dpaulb005/radar-dev-/3d/renders/drone/exploded.png

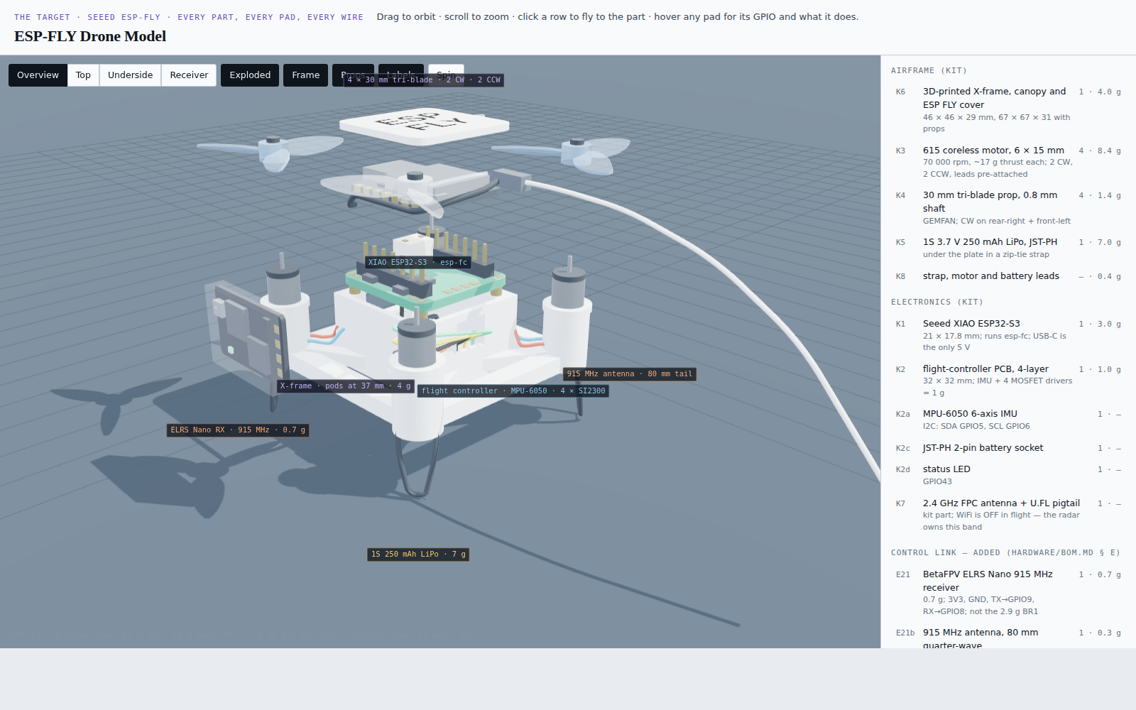
3d/renders/drone/exploded.png
