dpaulb005/radar-dev-/3d/renders/drone/receiver.png

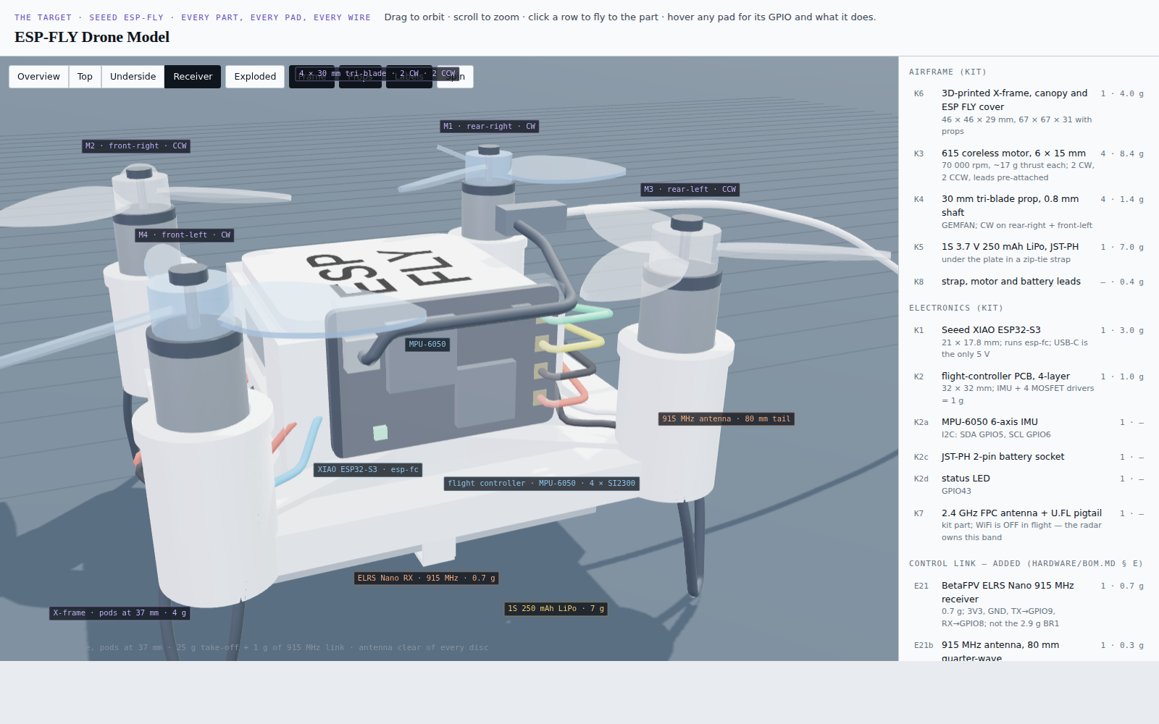
3d/renders/drone/receiver.png
