dpaulb005/radar-dev-/3d/renders/drone/top.png

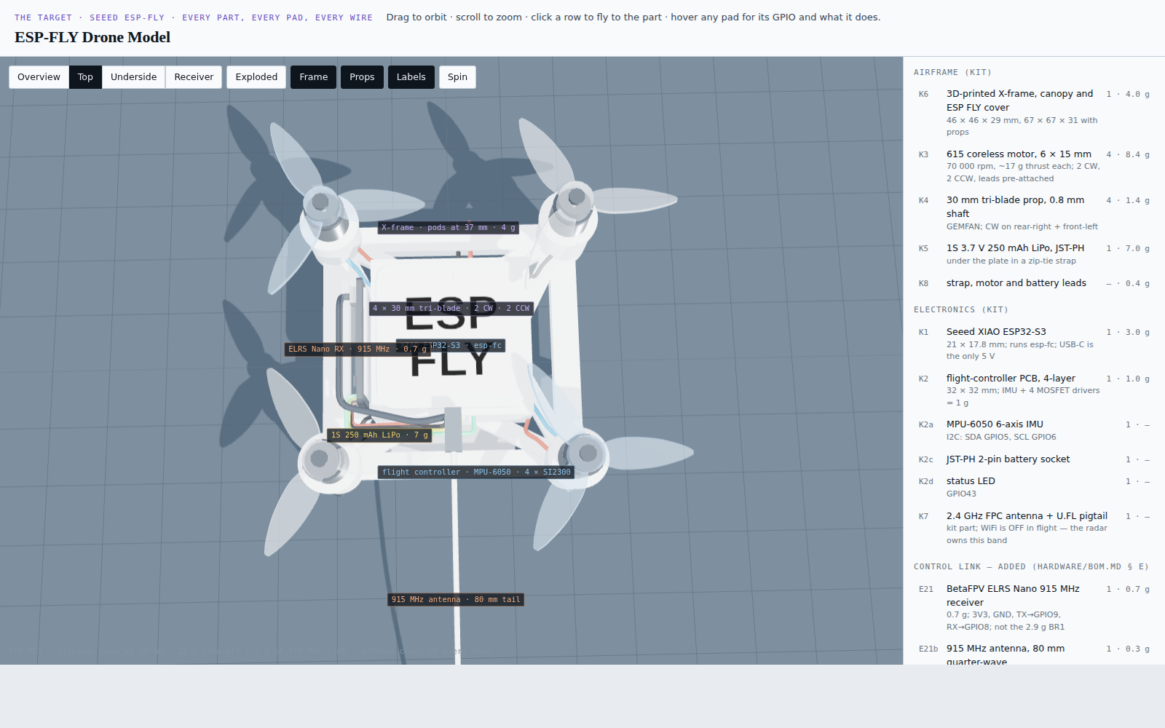
3d/renders/drone/top.png
