dpaulb005/radar-dev-/3d/renders/drone/underside.png

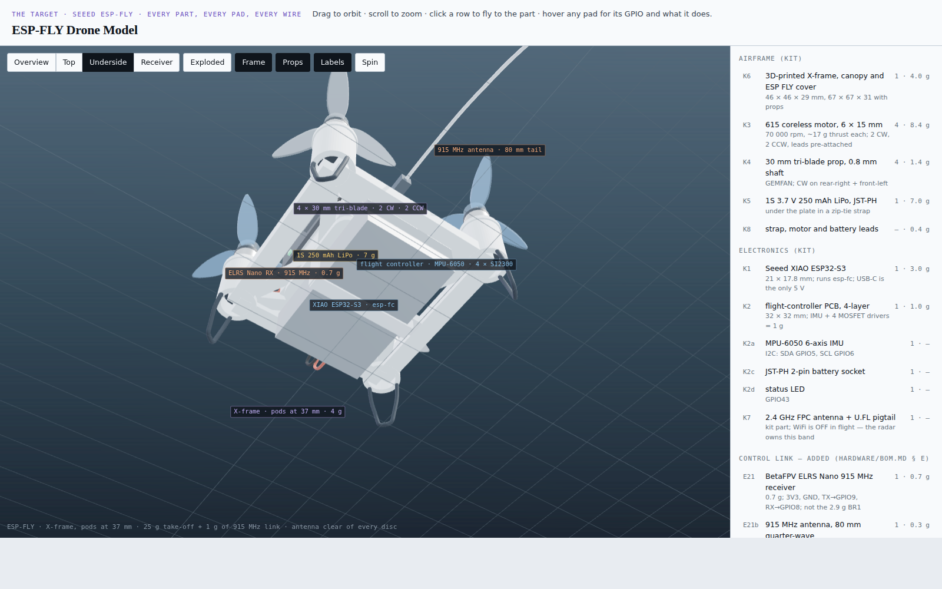
3d/renders/drone/underside.png
