dpaulb005/radar-dev-/3d/renders/radar-bench/bench.png

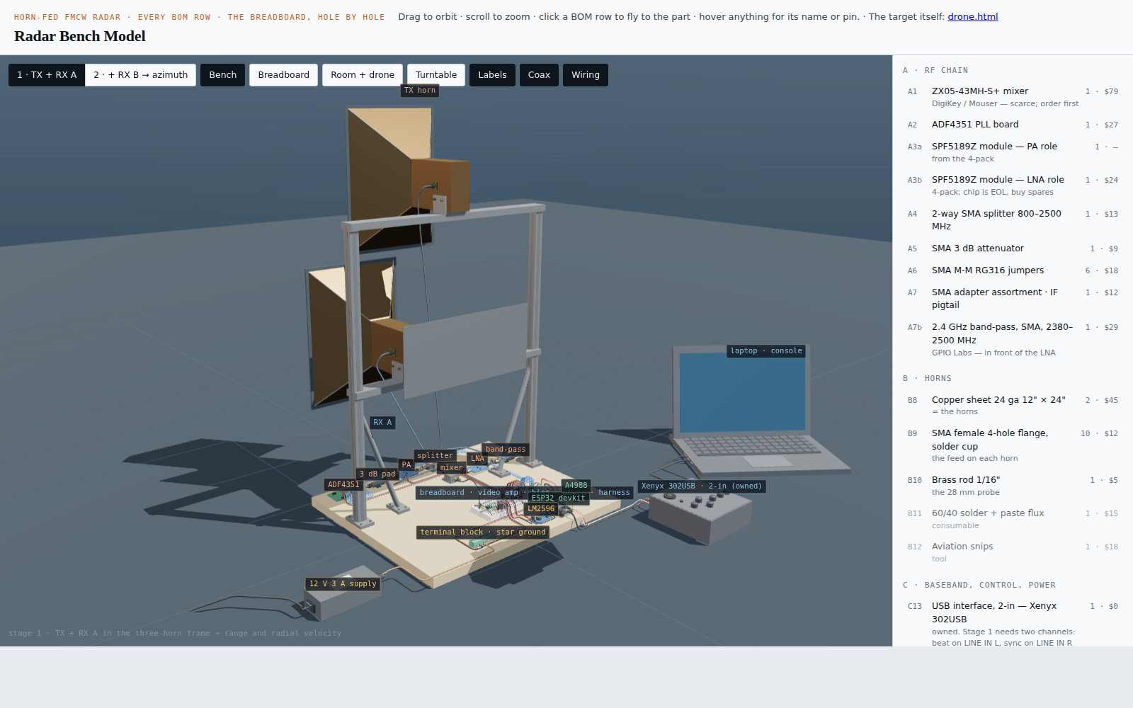
3d/renders/radar-bench/bench.png
