dpaulb005/radar-dev-/3d/renders/radar-bench/breadboard.png

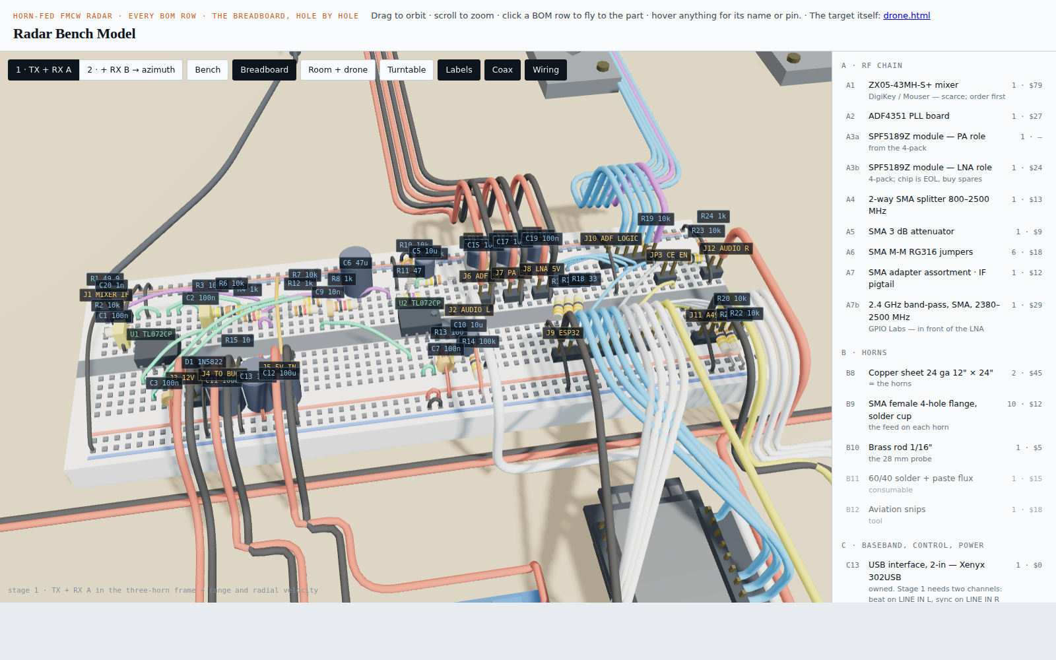
3d/renders/radar-bench/breadboard.png
