dpaulb005/radar-dev-/3d/renders/radar-bench/desk.png

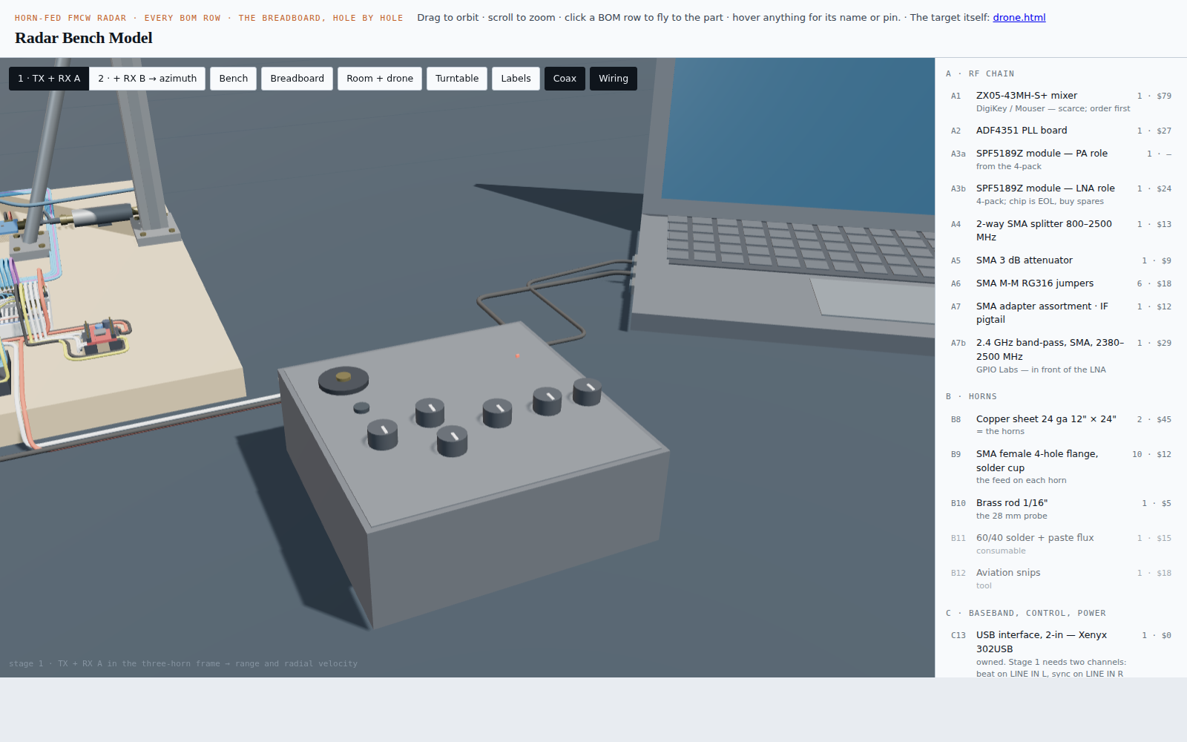
3d/renders/radar-bench/desk.png
