dpaulb005/radar-dev-/3d/renders/radar-bench/plan.png

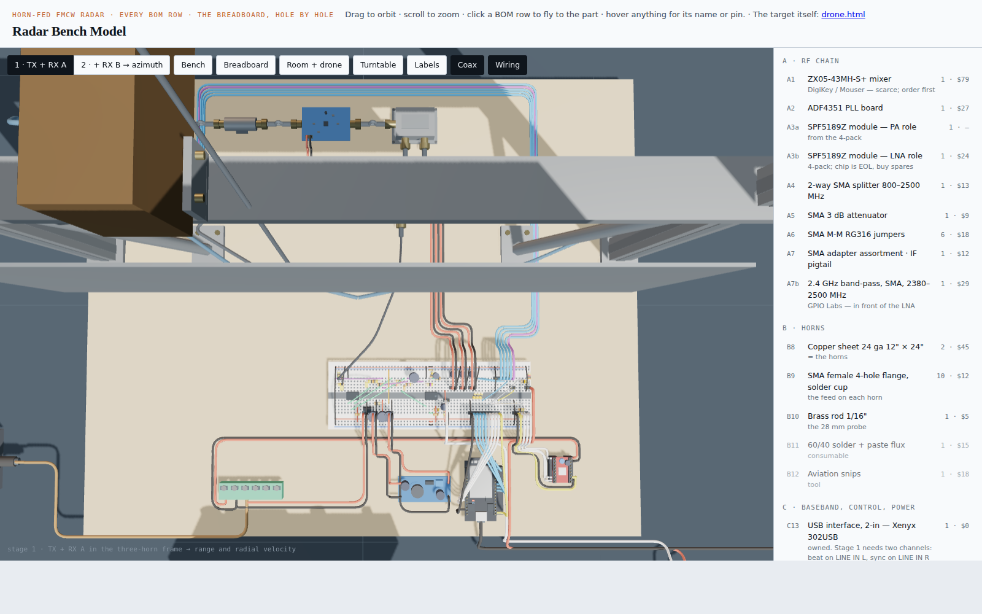
3d/renders/radar-bench/plan.png
