dpaulb005/radar-dev-/3d/renders/radar-bench/room.png

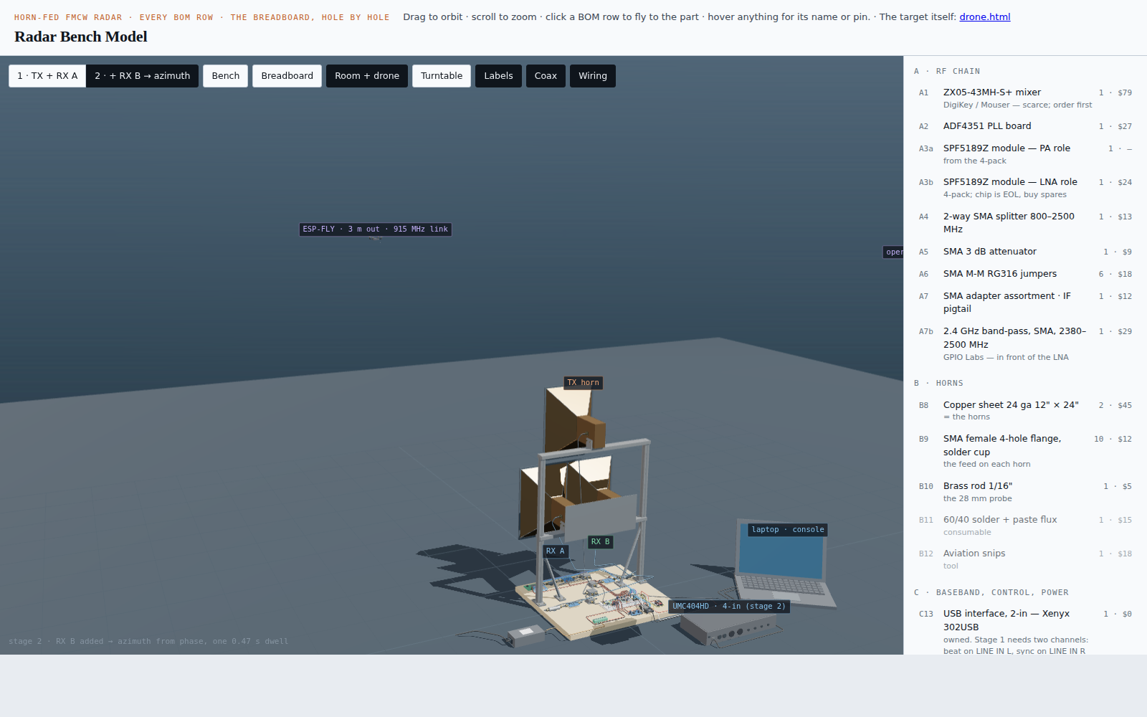
3d/renders/radar-bench/room.png
