dpaulb005/radar-dev-/3d/renders/radar-bench/stage2.png

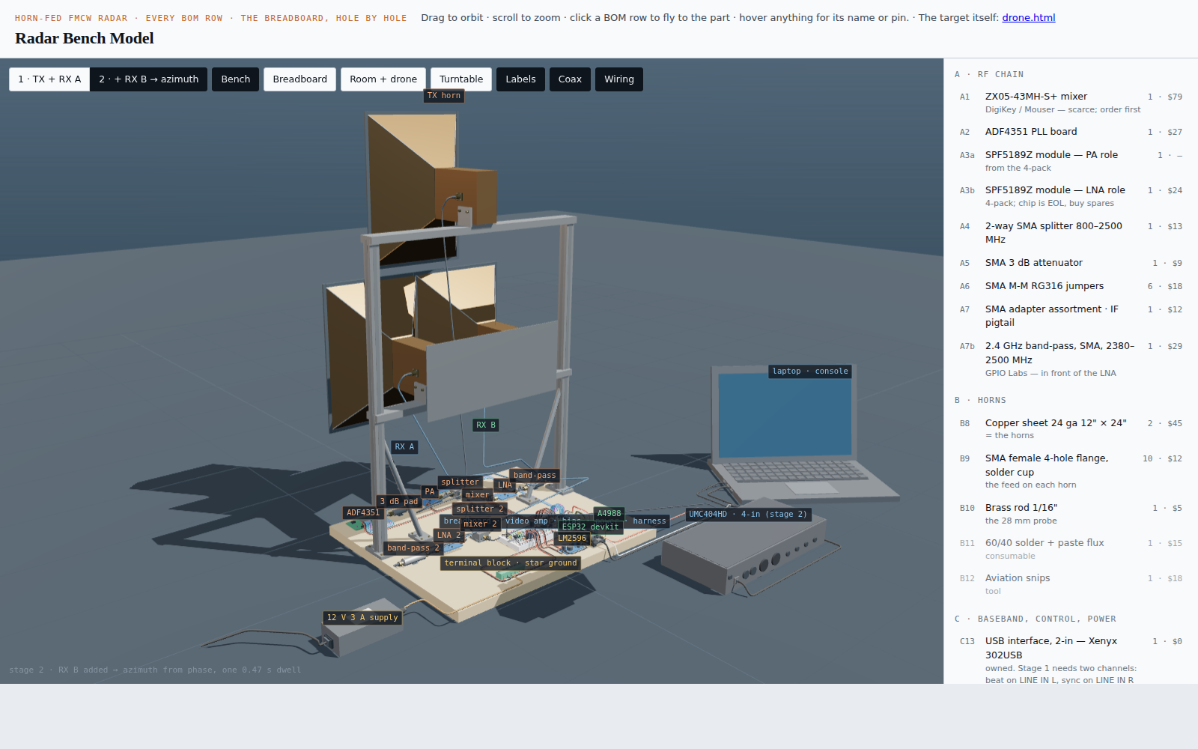
3d/renders/radar-bench/stage2.png
