dpaulb005/radar-dev-/breadboard/schematics/radar_flow.png

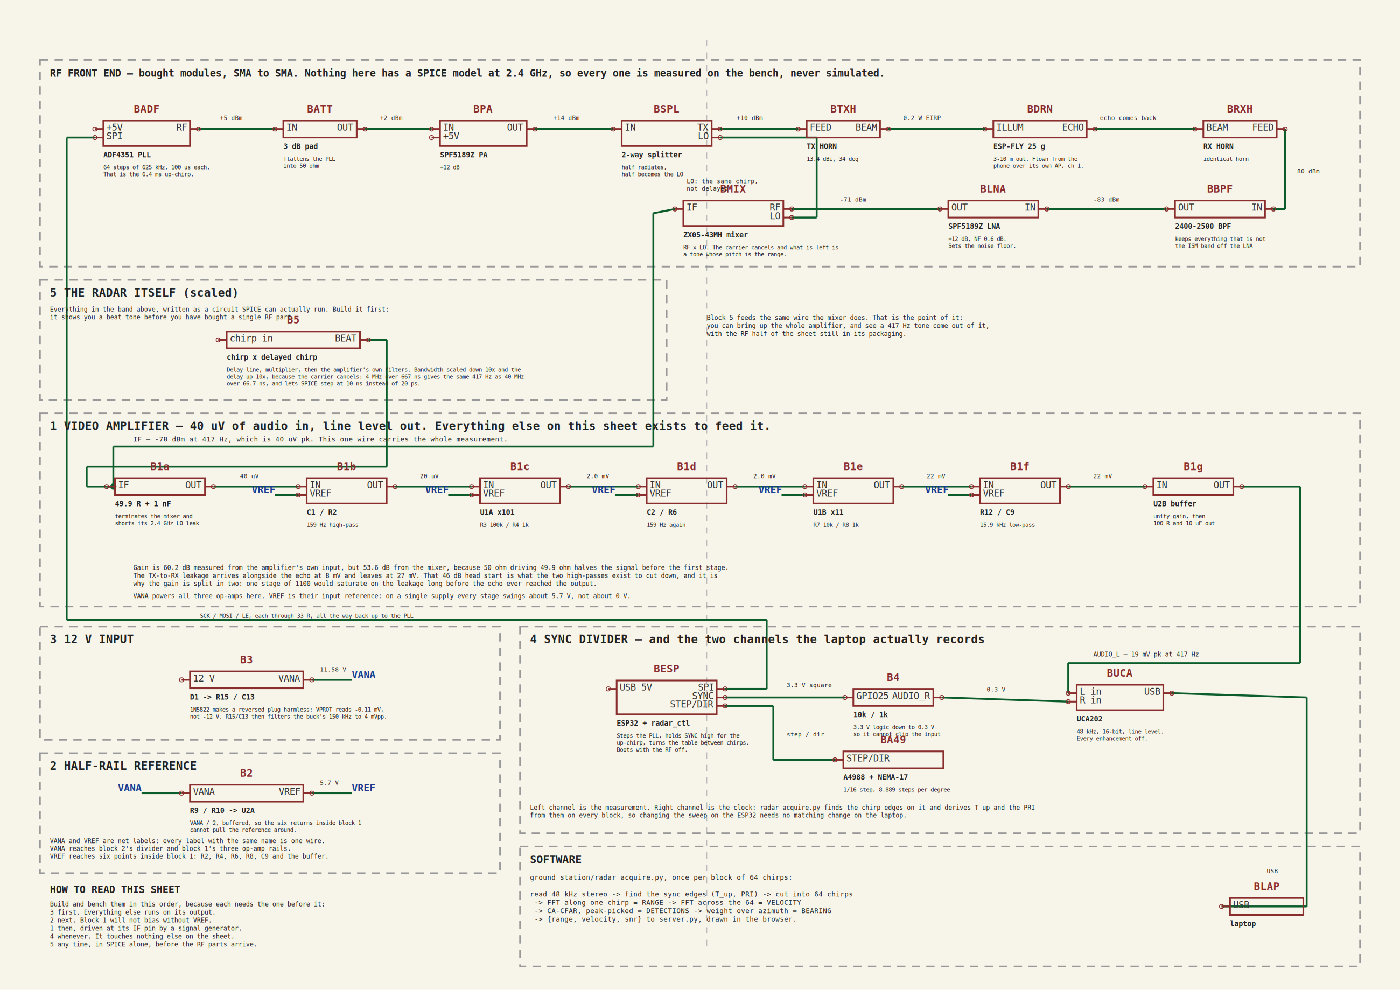
breadboard/schematics/radar_flow.png
