dpaulb005/radar-dev-/breadboard/schematics/radar_breadboard.kicad_sch

## KiCad design breadboard/schematics/radar_breadboard.kicad_sch (2026-09-09)

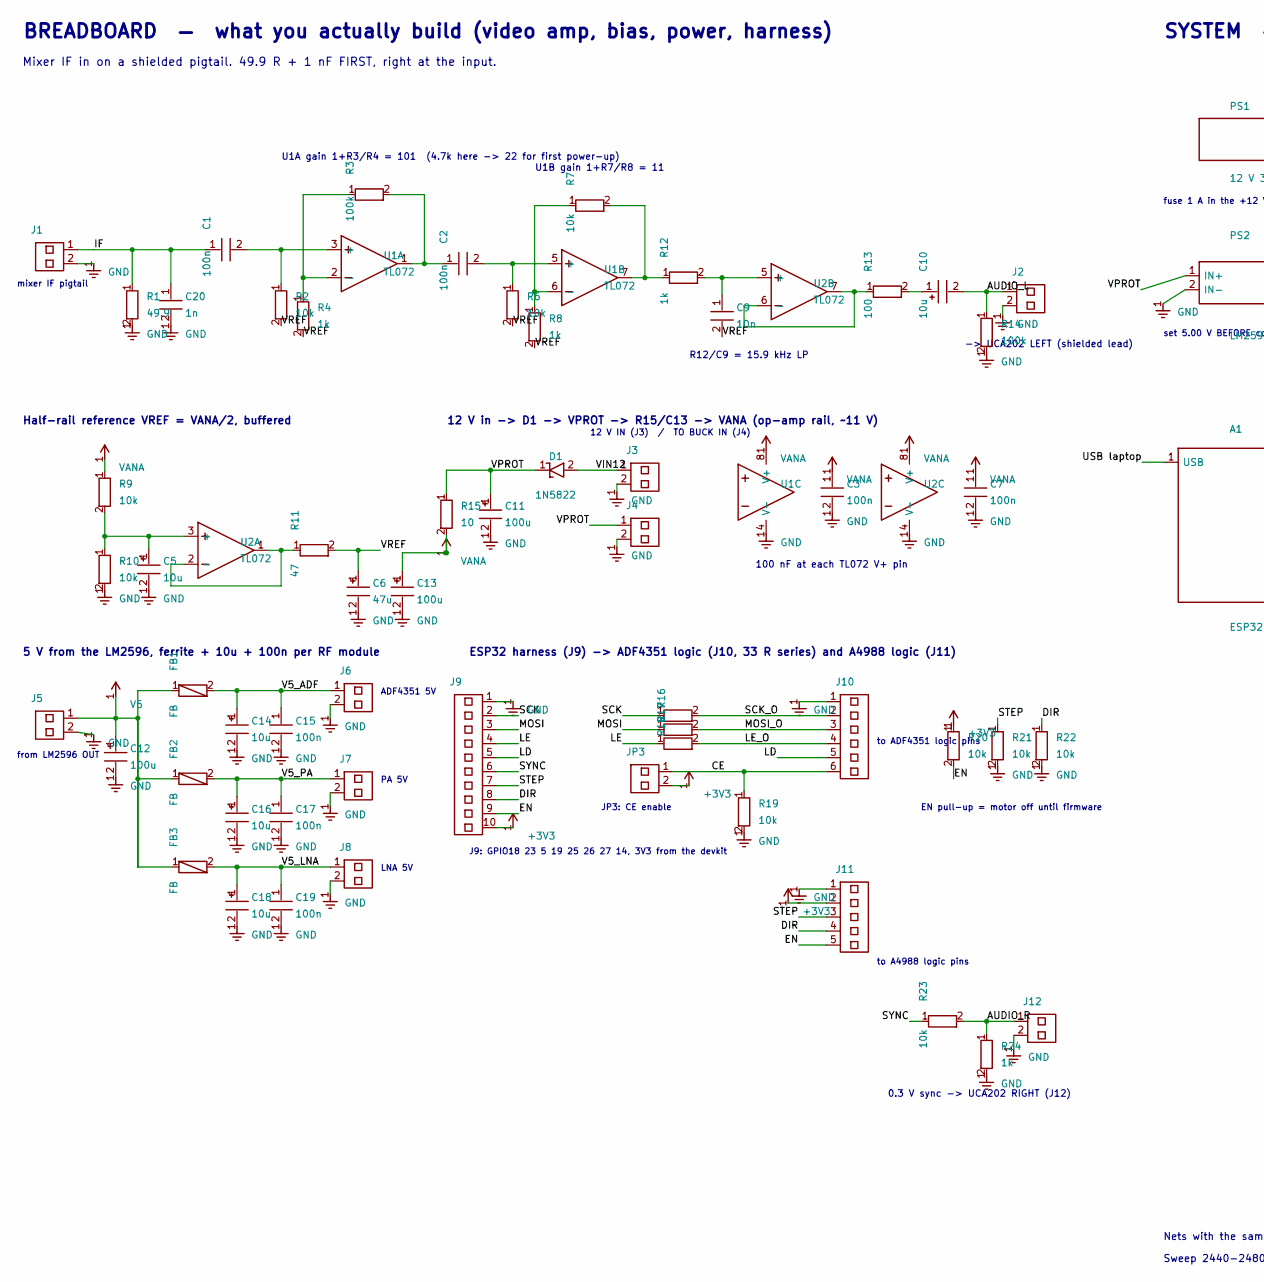
[picture p34: schematic radar_breadboard.kicad_sch, part in row 1, column 1]

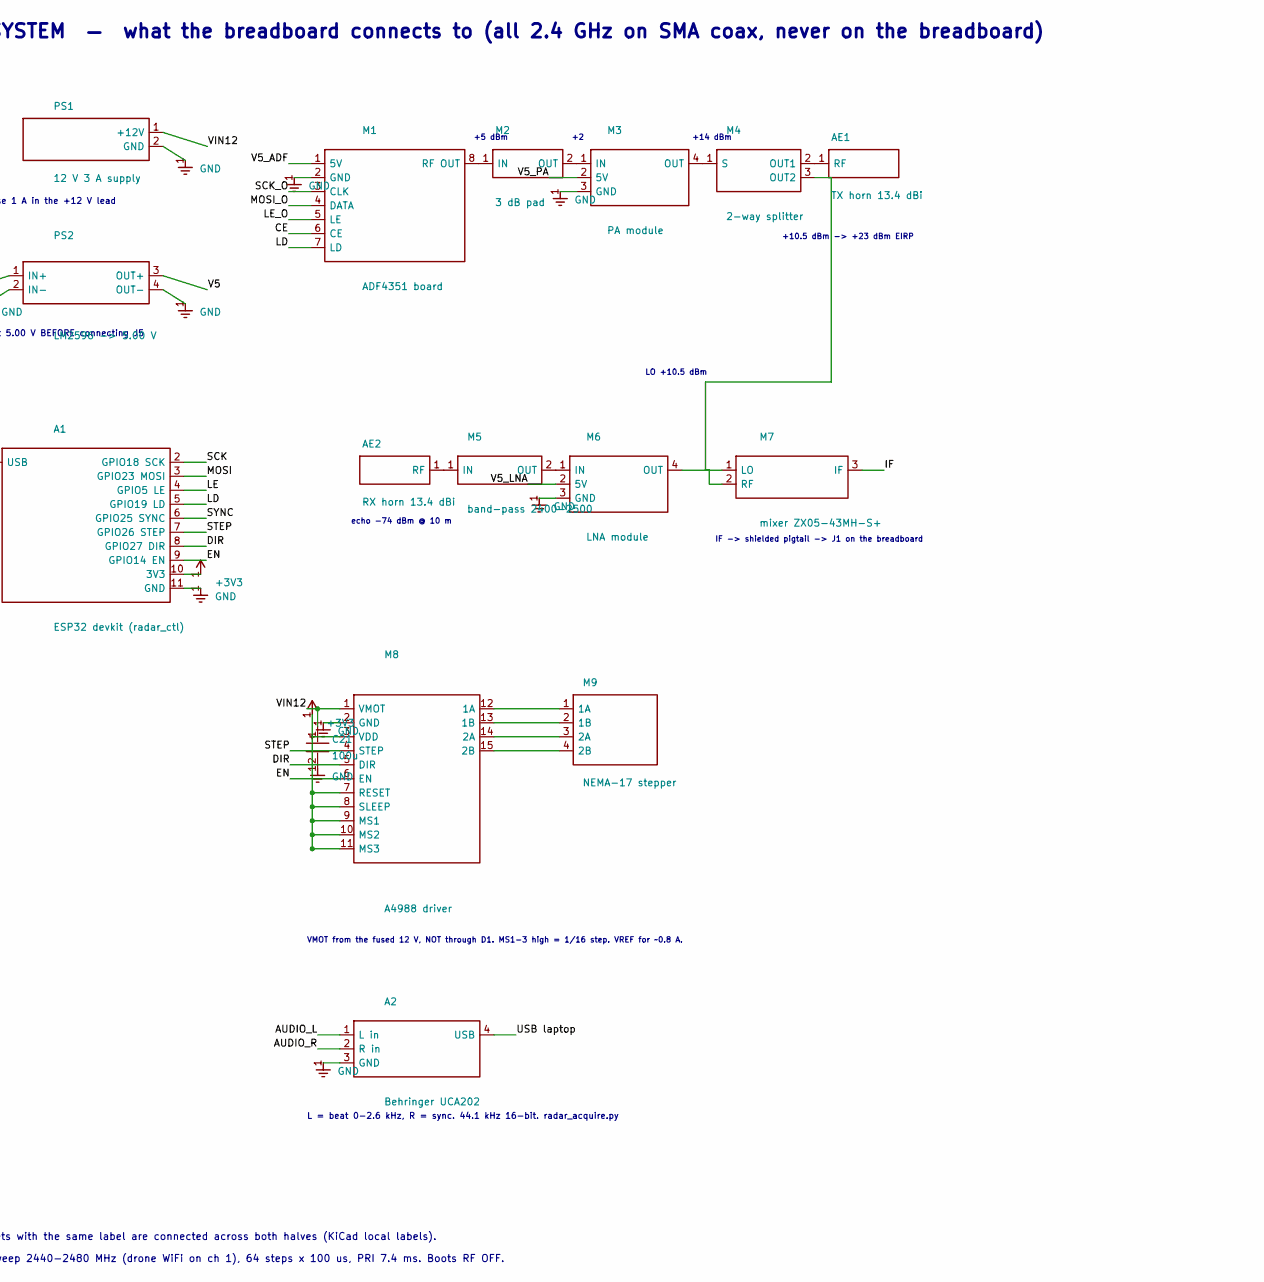
[picture p35: schematic radar_breadboard.kicad_sch, part in row 1, column 2]

Parts:
A1: ESP32 devkit (radar_ctl)
A2: Behringer UCA202
AE1: TX horn 13.4 dBi
AE2: RX horn 13.4 dBi
C1, C2, C3, C7, C15, C17, C19: 100n
C5, C10, C14, C16, C18: 10u
C6: 47u
C9: 10n
C11, C12, C13, C21: 100u
C20: 1n
D1: 1N5822
FB1, FB2, FB3: FB
J1: MIXER IF
J2: AUDIO L
J3: 12V IN
J4: TO BUCK IN
J5: FROM BUCK 5V
J6: ADF4351 5V
J7: PA 5V
J8: LNA 5V
J9: ESP32
J10: ADF LOGIC
J11: A4988 LOGIC
J12: AUDIO R
JP3: JP3 CE EN
M1: ADF4351 board
M2: 3 dB pad
M3: PA module
M4: 2-way splitter
M5: band-pass 2400-2500
M6: LNA module
M7: mixer ZX05-43MH-S+
M8: A4988 driver
M9: NEMA-17 stepper
PS1: 12 V 3 A supply
PS2: LM2596 -> 5.00 V
R1: 49.9
R2, R6, R7, R9, R10, R19, R20, R21, R22, R23: 10k
R3, R14: 100k
R4, R8, R12, R24: 1k
R11: 47
R13: 100
R15: 10
R16, R17, R18: 33
U1, U2: TL072

Connections:
+3V3: A1.10 (3V3), J9.10, J11.2, JP3.2, M8.3 (VDD), M8.7 (RESET), M8.8 (SLEEP), M8.9 (MS1), M8.10 (MS2), M8.11 (MS3), R20.1
AUDIO_L: A2.1 (L in), C10.2, J2.1, R14.1
AUDIO_R: A2.2 (R in), J12.1, R23.2, R24.1
CE: J10.6, JP3.1, M1.6 (CE), R19.1
DIR: A1.8 (GPIO27 DIR), J9.8, J11.4, M8.5 (DIR), R22.1
EN: A1.9 (GPIO14 EN), J9.9, J11.5, M8.6 (EN), R20.2
GND: A1.11 (GND), A2.3 (GND), C3.2, C5.2, C6.2, C7.2, C11.2, C12.2, C13.2, C14.2, C15.2, C16.2, C17.2, C18.2, C19.2, C20.2, C21.2, J1.2, J2.2, J3.2, J4.2, J5.2, J6.2, J7.2, J8.2, J9.1, J10.1, J11.1, J12.2, M1.2 (GND), M3.3 (GND), M6.3 (GND), M8.2 (GND), PS1.2 (GND), PS2.2 (IN-), PS2.4 (OUT-), R1.2, R10.2, R14.2, R19.2, R21.2, R22.2, R24.2, U1.4 (V-), U2.4 (V-)
IF: C1.1, C20.1, J1.1, M7.3 (IF), R1.1
LD: A1.5 (GPIO19 LD), J9.5, J10.5, M1.7 (LD)
LE: A1.4 (GPIO5 LE), J9.4, R18.1
LE_O: J10.4, M1.5 (LE), R18.2
MOSI: A1.3 (GPIO23 MOSI), J9.3, R17.1
MOSI_O: J10.3, M1.4 (DATA), R17.2
unnamed: AE1.1, M4.2 (OUT1)
unnamed: AE2.1, M5.1 (IN)
unnamed: C1.2, R2.1, U1.3 (+)
unnamed: C2.1, R3.2, U1.1
unnamed: C2.2, R6.1, U1.5 (+)
unnamed: C5.1, R9.2, R10.1, U2.3 (+)
unnamed: C9.1, R12.2, U2.5 (+)
unnamed: C10.1, R13.2
unnamed: M1.8 (RF OUT), M2.1 (IN)
unnamed: M2.2 (OUT), M3.1 (IN)
unnamed: M3.4 (OUT), M4.1 (S)
unnamed: M4.3 (OUT2), M7.1 (LO)
unnamed: M5.2 (OUT), M6.1 (IN)
unnamed: M6.4 (OUT), M7.2 (RF)
unnamed: M8.12 (1A), M9.1 (1A)
unnamed: M8.13 (1B), M9.2 (1B)
unnamed: M8.14 (2A), M9.3 (2A)
unnamed: M8.15 (2B), M9.4 (2B)
unnamed: R3.1, R4.1, U1.2 (-)
unnamed: R7.1, R8.1, U1.6 (-)
unnamed: R11.1, U2.1, U2.2 (-)
unnamed: R7.2, R12.1, U1.7
unnamed: R13.1, U2.6 (-), U2.7
SCK: A1.2 (GPIO18 SCK), J9.2, R16.1
SCK_O: J10.2, M1.3 (CLK), R16.2
STEP: A1.7 (GPIO26 STEP), J9.7, J11.3, M8.4 (STEP), R21.1
SYNC: A1.6 (GPIO25 SYNC), J9.6, R23.1
USB laptop: A1.1 (USB), A2.4 (USB)
V5: C12.1, FB1.1, FB2.1, FB3.1, J5.1, PS2.3 (OUT+)
V5_ADF: C14.1, C15.1, FB1.2, J6.1, M1.1 (5V)
V5_LNA: C18.1, C19.1, FB3.2, J8.1, M6.2 (5V)
V5_PA: C16.1, C17.1, FB2.2, J7.1, M3.2 (5V)
VANA: C3.1, C7.1, C13.1, R9.1, R15.2, U1.8 (V+), U2.8 (V+)
VIN12: C21.1, D1.2 (A), J3.1, M8.1 (VMOT), PS1.1 (+12V)
VPROT: C11.1, D1.1 (K), J4.1, PS2.1 (IN+), R15.1
VREF: C6.1, C9.2, R2.2, R4.2, R6.2, R8.2, R11.2

Notes on the sheet:
BREADBOARD — what you actually build (video amp, bias, power, harness)
Mixer IF in on a shielded pigtail. 49.9 R + 1 nF FIRST, right at the input.
mixer IF pigtail
U1A gain 1+R3/R4 = 101 (4.7k here -> 22 for first power-up)
U1B gain 1+R7/R8 = 11
R12/C9 = 15.9 kHz LP
-> UCA202 LEFT (shielded lead)
Half-rail reference VREF = VANA/2, buffered
12 V in -> D1 -> VPROT -> R15/C13 -> VANA (op-amp rail, ~11 V)
12 V IN (J3) / TO BUCK IN (J4)
100 nF at each TL072 V+ pin
5 V from the LM2596, ferrite + 10u + 100n per RF module
from LM2596 OUT
ADF4351 5V
PA 5V
LNA 5V
ESP32 harness (J9) -> ADF4351 logic (J10, 33 R series) and A4988 logic (J11)
J9: GPIO18 23 5 19 25 26 27 14, 3V3 from the devkit
to ADF4351 logic pins
JP3: CE enable
to A4988 logic pins
EN pull-up = motor off until firmware
0.3 V sync -> UCA202 RIGHT (J12)
SYSTEM — what the breadboard connects to (all 2.4 GHz on SMA coax, never on the breadboard)
fuse 1 A in the +12 V lead
set 5.00 V BEFORE connecting J5
+5 dBm
+14 dBm
+10.5 dBm -> +23 dBm EIRP
LO +10.5 dBm
IF -> shielded pigtail -> J1 on the breadboard
echo -74 dBm @ 10 m
VMOT from the fused 12 V, NOT through D1. MS1-3 high = 1/16 step. VREF for ~0.8 A.
L = beat 0-2.6 kHz, R = sync. 44.1 kHz 16-bit. radar_acquire.py
Nets with the same label are connected across both halves (KiCad local labels).
Sweep 2440-2480 MHz (drone WiFi on ch 1), 64 steps x 100 us, PRI 7.4 ms. Boots RF OFF.
