dpaulb005/radar-dev-/breadboard/schematics/radar_flow.kicad_sch

## KiCad design breadboard/schematics/radar_flow.kicad_sch (2026-09-09)

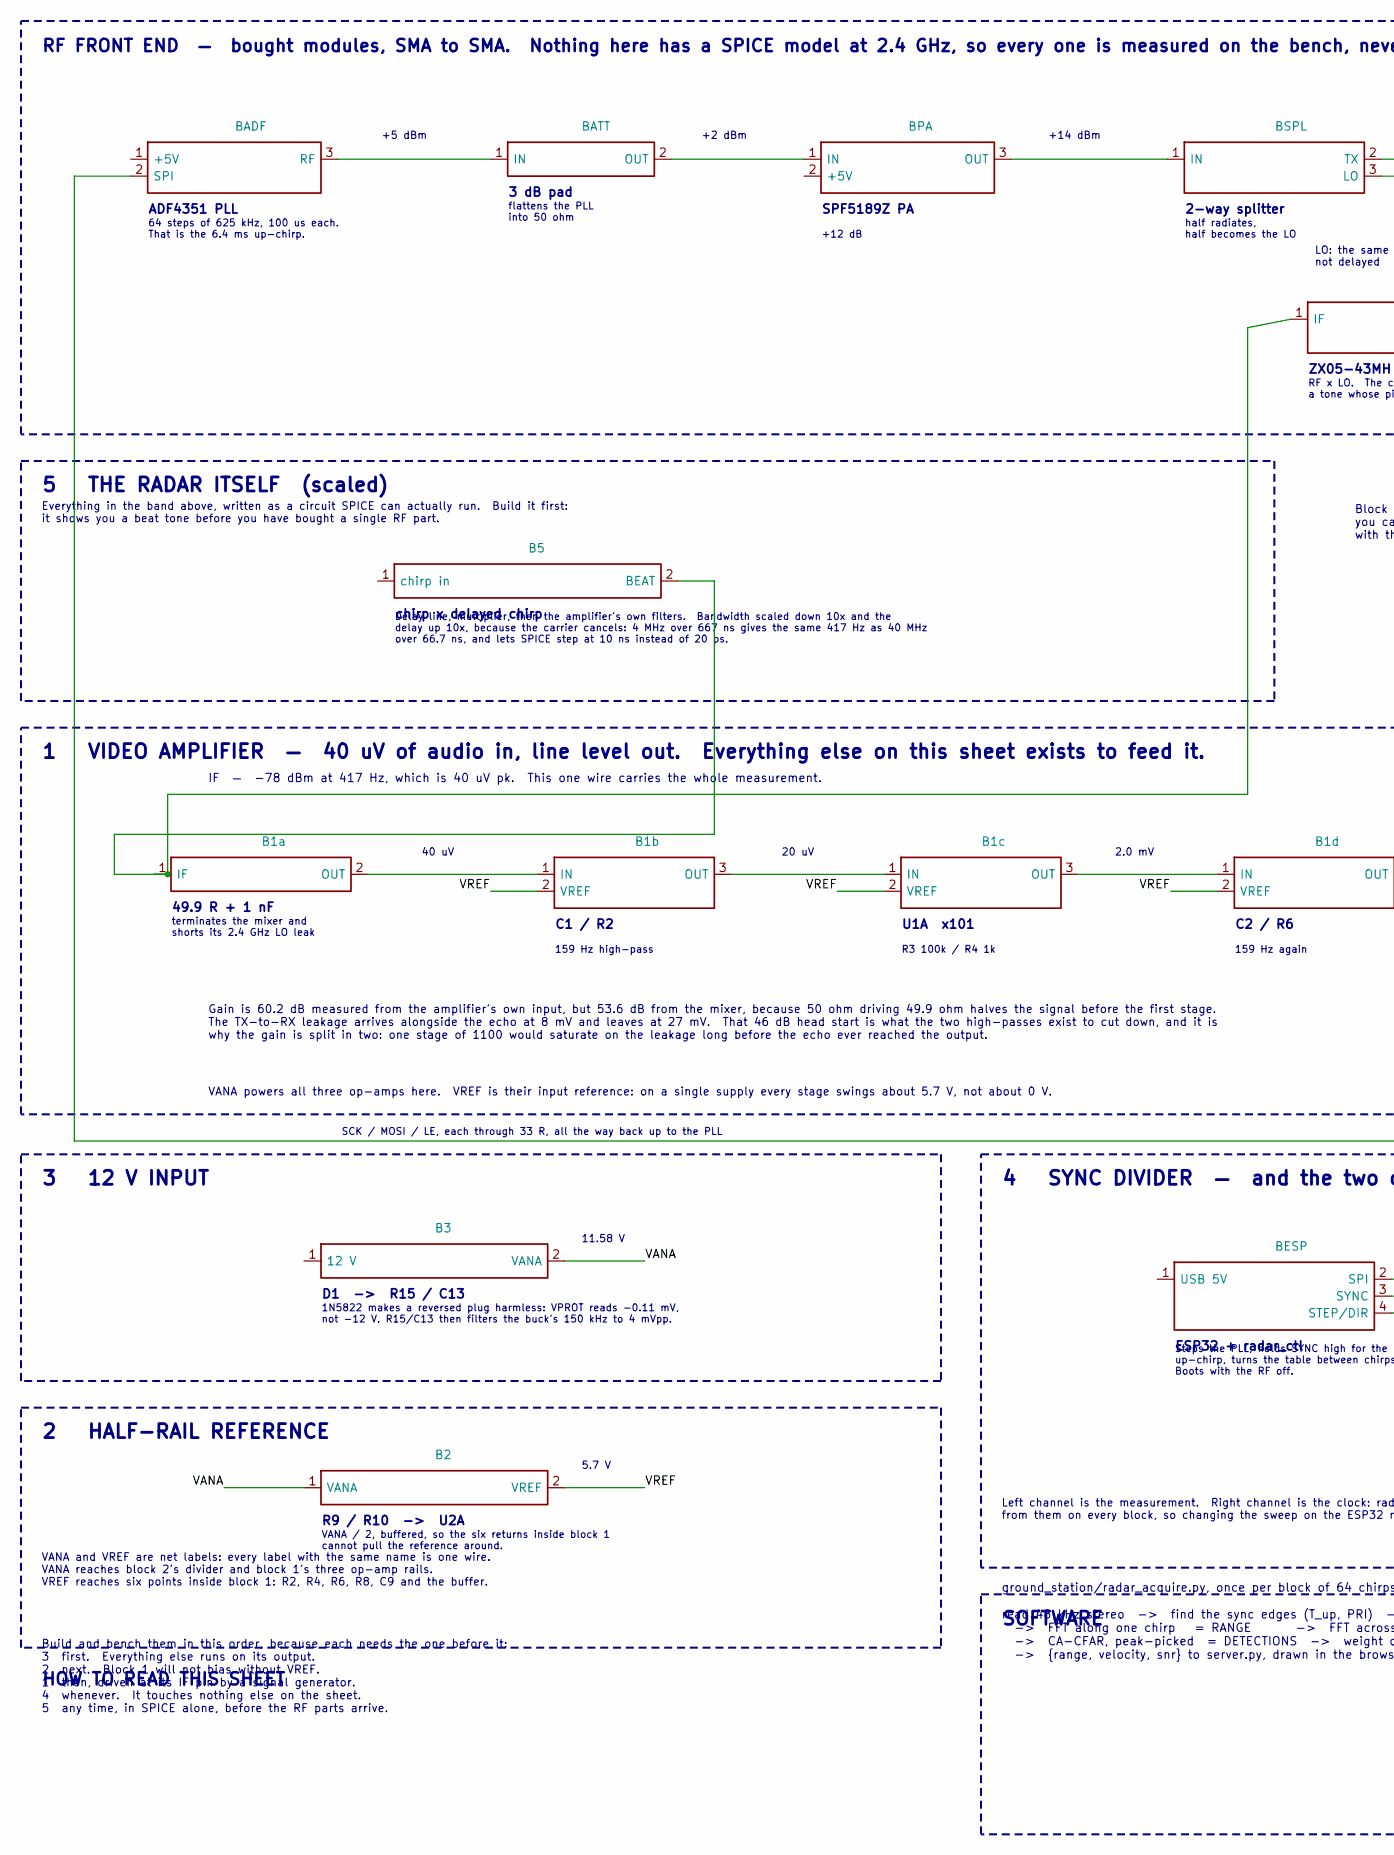
[picture p36: schematic radar_flow.kicad_sch, part in row 1, column 1]

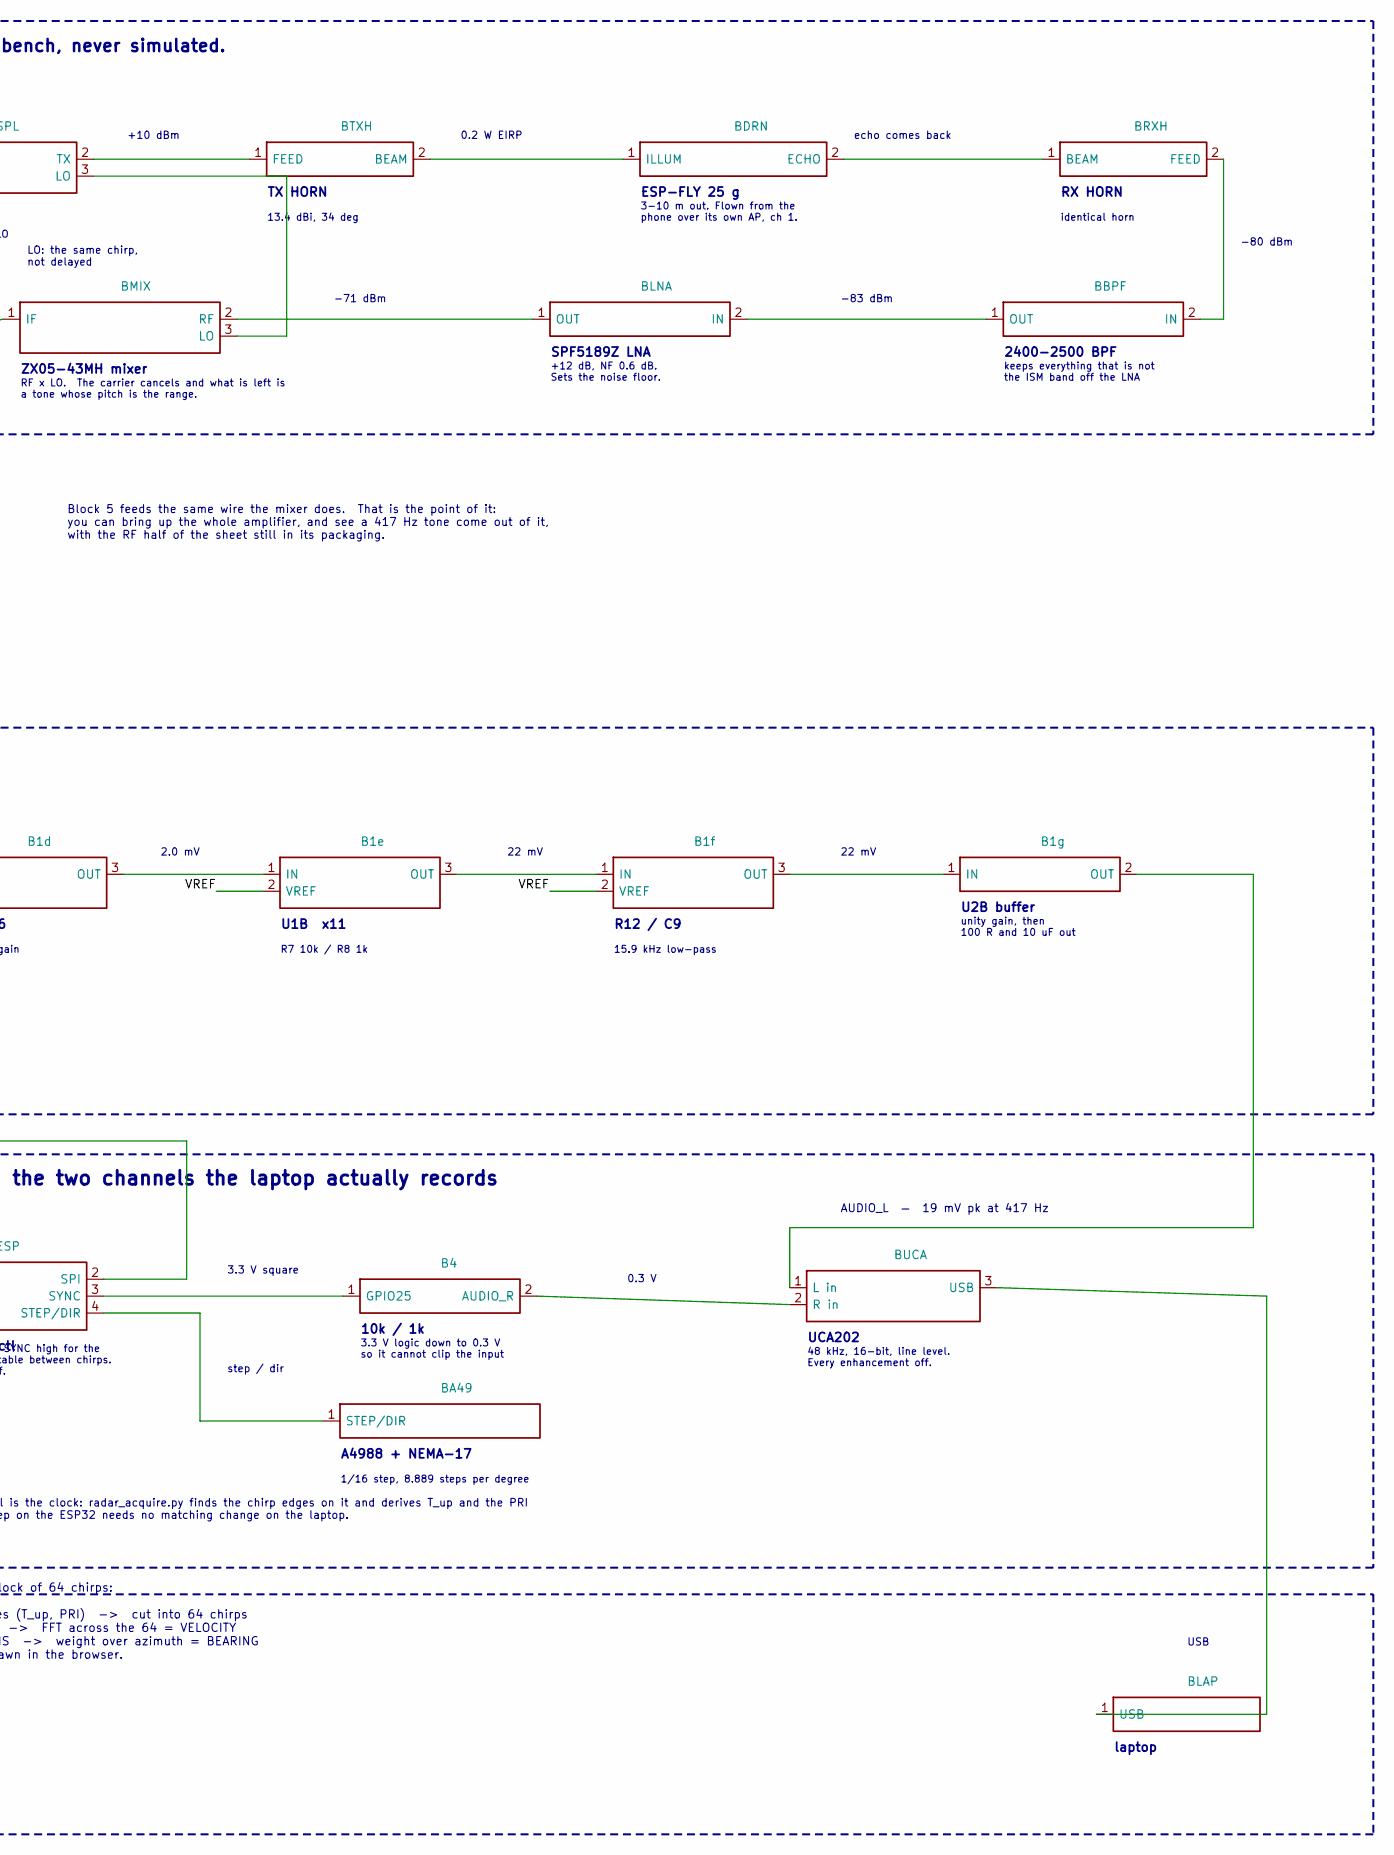
[picture p37: schematic radar_flow.kicad_sch, part in row 1, column 2]

Parts:
B1a: 49.9 R + 1 nF
B1b: C1 / R2
B1c: U1A x101
B1d: C2 / R6
B1e: U1B x11
B1f: R12 / C9
B1g: U2B buffer
B2: R9 / R10 -> U2A
B3: D1 -> R15 / C13
B4: 10k / 1k
B5: chirp x delayed chirp
BA49: A4988 + NEMA-17
BADF: ADF4351 PLL
BATT: 3 dB pad
BBPF: 2400-2500 BPF
BDRN: ESP-FLY 25 g
BESP: ESP32 + radar_ctl
BLAP: laptop
BLNA: SPF5189Z LNA
BMIX: ZX05-43MH mixer
BPA: SPF5189Z PA
BRXH: RX HORN
BSPL: 2-way splitter
BTXH: TX HORN
BUCA: UCA202

Connections:
unnamed: B1a.1 (IF), B5.2 (BEAT), BMIX.1 (IF)
unnamed: B1a.2 (OUT), B1b.1 (IN)
unnamed: B1b.3 (OUT), B1c.1 (IN)
unnamed: B1c.3 (OUT), B1d.1 (IN)
unnamed: B1d.3 (OUT), B1e.1 (IN)
unnamed: B1e.3 (OUT), B1f.1 (IN)
unnamed: B1f.3 (OUT), B1g.1 (IN)
unnamed: B1g.2 (OUT), BUCA.1 (L in)
unnamed: B4.1 (GPIO25), BESP.3 (SYNC)
unnamed: B4.2 (AUDIO_R), BUCA.2 (R in)
unnamed: BA49.1, BESP.4 (STEP/DIR)
unnamed: BADF.2 (SPI), BESP.2 (SPI)
unnamed: BADF.3 (RF), BATT.1 (IN)
unnamed: BATT.2 (OUT), BPA.1 (IN)
unnamed: BBPF.1 (OUT), BLNA.2 (IN)
unnamed: BBPF.2 (IN), BRXH.2 (FEED)
unnamed: BDRN.1 (ILLUM), BTXH.2 (BEAM)
unnamed: BDRN.2 (ECHO), BRXH.1 (BEAM)
unnamed: BLAP.1, BUCA.3 (USB)
unnamed: BLNA.1 (OUT), BMIX.2 (RF)
unnamed: BMIX.3 (LO), BSPL.3 (LO)
unnamed: BPA.3 (OUT), BSPL.1 (IN)
unnamed: BSPL.2 (TX), BTXH.1 (FEED)
VANA: B2.1 (VANA), B3.2 (VANA)
VREF: B1b.2 (VREF), B1c.2 (VREF), B1d.2 (VREF), B1e.2 (VREF), B1f.2 (VREF), B2.2 (VREF)

Notes on the sheet:
RF FRONT END — bought modules, SMA to SMA. Nothing here has a SPICE model at 2.4 GHz, so every one is measured on the bench, never simulated.
ADF4351 PLL
64 steps of 625 kHz, 100 us each. That is the 6.4 ms up-chirp.
3 dB pad
flattens the PLL into 50 ohm
SPF5189Z PA
+12 dB
2-way splitter
half radiates, half becomes the LO
TX HORN
13.4 dBi, 34 deg
ESP-FLY 25 g
3-10 m out. Flown from the phone over its own AP, ch 1.
RX HORN
identical horn
+5 dBm
+2 dBm
+14 dBm
+10 dBm
0.2 W EIRP
echo comes back
ZX05-43MH mixer
RF x LO. The carrier cancels and what is left is a tone whose pitch is the range.
SPF5189Z LNA
+12 dB, NF 0.6 dB. Sets the noise floor.
2400-2500 BPF
keeps everything that is not the ISM band off the LNA
-80 dBm
-83 dBm
-71 dBm
LO: the same chirp, not delayed
5 THE RADAR ITSELF (scaled)
Everything in the band above, written as a circuit SPICE can actually run. Build it first: it shows you a beat tone before you have bought a single RF part.
chirp x delayed chirp
Delay line, multiplier, then the amplifier's own filters. Bandwidth scaled down 10x and the delay up 10x, because the carrier cancels: 4 MHz over 667 ns gives the same 417 Hz as 40 MHz over 66.7 ns, and lets SPICE step at 10 ns instead of 20 ps.
1 VIDEO AMPLIFIER — 40 uV of audio in, line level out. Everything else on this sheet exists to feed it.
49.9 R + 1 nF
terminates the mixer and shorts its 2.4 GHz LO leak
C1 / R2
159 Hz high-pass
U1A x101
R3 100k / R4 1k
C2 / R6
159 Hz again
U1B x11
R7 10k / R8 1k
R12 / C9
15.9 kHz low-pass
U2B buffer
unity gain, then 100 R and 10 uF out
IF — -78 dBm at 417 Hz, which is 40 uV pk. This one wire carries the whole measurement.
Block 5 feeds the same wire the mixer does. That is the point of it: you can bring up the whole amplifier, and see a 417 Hz tone come out of it, with the RF half of the sheet still in its packaging.
40 uV
20 uV
2.0 mV
22 mV
Gain is 60.2 dB measured from the amplifier's own input, but 53.6 dB from the mixer, because 50 ohm driving 49.9 ohm halves the signal before the first stage. The TX-to-RX leakage arrives alongside the echo at 8 mV and leaves at 27 mV. That 46 dB head start is what the two high-passes exist to cut 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
VANA powers all three op-amps here. VREF is their input reference: on a single supply every stage swings about 5.7 V, not about 0 V.
3 12 V INPUT
D1 -> R15 / C13
1N5822 makes a reversed plug harmless: VPROT reads -0.11 mV, not -12 V. R15/C13 then filters the buck's 150 kHz to 4 mVpp.
11.58 V
2 HALF-RAIL REFERENCE
R9 / R10 -> U2A
VANA / 2, buffered, so the six returns inside block 1 cannot pull the reference around.
5.7 V
VANA and VREF are net labels: every label with the same name is one wire. VANA reaches block 2's divider and block 1's three op-amp rails. VREF reaches six points inside block 1: R2, R4, R6, R8, C9 and the buffer.
4 SYNC DIVIDER — and the two channels the laptop actually records
ESP32 + radar_ctl
Steps the PLL, holds SYNC high for the up-chirp, turns the table between chirps. Boots with the RF off.
10k / 1k
3.3 V logic down to 0.3 V so it cannot clip the input
UCA202
48 kHz, 16-bit, line level. Every enhancement off.
A4988 + NEMA-17
1/16 step, 8.889 steps per degree
3.3 V square
0.3 V
step / dir
SCK / MOSI / LE, each through 33 R, all the way back up to the PLL
AUDIO_L — 19 mV pk at 417 Hz
Left channel is the measurement. Right channel is the clock: radar_acquire.py finds the chirp edges on it and derives T_up and the PRI from them on every block, so changing the sweep on the ESP32 needs no matching change on the laptop.
SOFTWARE
laptop
USB
ground_station/radar_acquire.py, once per block of 64 chirps: read 48 kHz stereo -> find the sync edges (T_up, PRI) -> cut into 64 chirps -> FFT along one chirp = RANGE -> FFT across the 64 = VELOCITY -> CA-CFAR, peak-picked = DETECTIONS -> weight over azimuth = BEARING -> {range, velocity, snr} to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
HOW TO READ THIS SHEET
Build and bench them in this order, because each needs the one before it: 3 first. Everything else runs on its output. 2 next. Block 1 will not bias without VREF. 1 then, driven at its IF pin by a signal generator. 4 whenever. It touches nothing else on the sheet. 5 any time, in SPICE alone, before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
