dpaulb005/radar-dev-/breadboard/schematics/radar_multisim.kicad_sch

## KiCad design breadboard/schematics/radar_multisim.kicad_sch (2026-09-09)

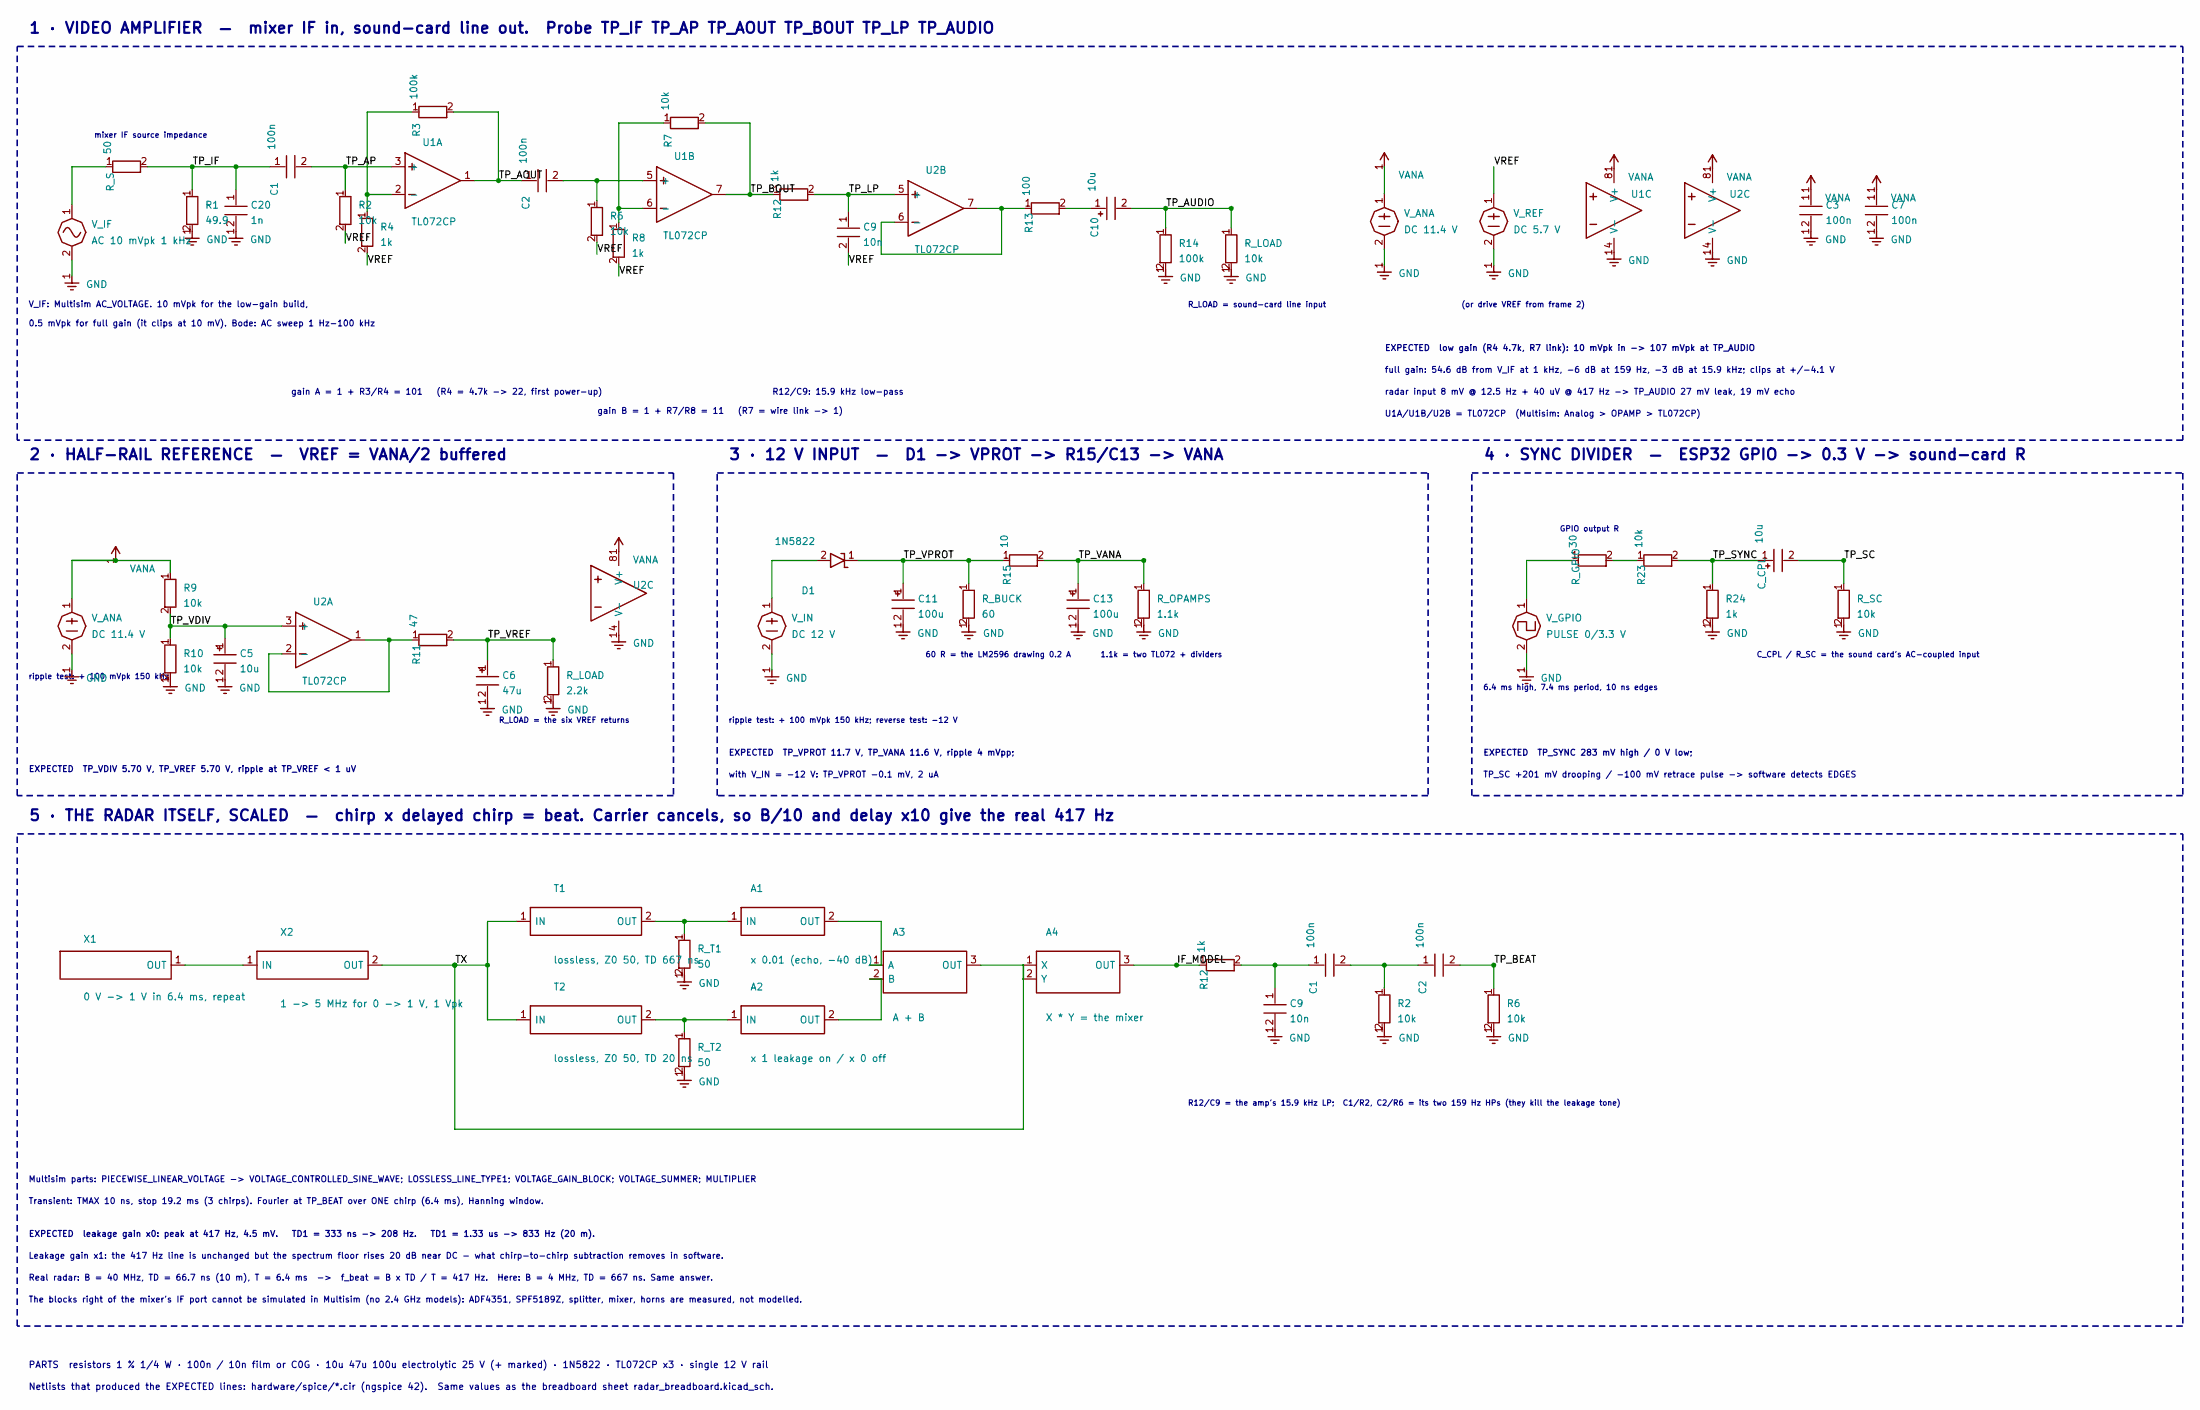
[picture p38: schematic radar_multisim.kicad_sch]

Parts:
A1: x 0.01 (echo, -40 dB)
A2: x 1 leakage on / x 0 off
A3: A + B
A4: X * Y = the mixer
C1, C2, C3, C7: 100n
C5, C10: 10u
C6: 47u
C9: 10n
C11, C13: 100u
C20: 1n
C_CPL: 10u
D1: 1N5822
R1: 49.9
R2, R6, R7, R9, R10, R23: 10k
R3, R14: 100k
R4, R8, R12, R24: 1k
R11: 47
R13: 100
R15: 10
R_BUCK: 60
R_GPIO: 30
R_LOAD: 10k
R_OPAMPS: 1.1k
R_S: 50
R_SC: 10k
R_T1, R_T2: 50
T1: lossless, Z0 50, TD 667 ns
T2: lossless, Z0 50, TD 20 ns
U1, U2: TL072CP
V_ANA: DC 11.4 V
V_GPIO: PULSE 0/3.3 V
V_IF: AC 10 mVpk 1 kHz
V_IN: DC 12 V
V_REF: DC 5.7 V
X1: 0 V -> 1 V in 6.4 ms, repeat
X2: 1 -> 5 MHz for 0 -> 1 V, 1 Vpk

Connections:
GND: C3.2, C5.2, C6.2, C7.2, C9.2, C11.2, C13.2, C20.2, R1.2, R2.2, R6.2, R10.2, R14.2, R24.2, R_BUCK.2, R_LOAD.2, R_OPAMPS.2, R_SC.2, R_T1.2, R_T2.2, U1.4 (V-), U2.4 (V-), V_ANA.2 (-), V_GPIO.2 (-), V_IF.2 (-), V_IN.2 (-), V_REF.2 (-)
IF_MODEL: A4.3 (OUT), R12.1
unnamed: A1.1 (IN), R_T1.1, T1.2 (OUT)
unnamed: A1.2 (OUT), A3.1 (A)
unnamed: A2.1 (IN), R_T2.1, T2.2 (OUT)
unnamed: A2.2 (OUT), A3.2 (B)
unnamed: C1.1, C9.1, R12.2
unnamed: C1.2, C2.1, R2.1
unnamed: C2.2, R6.1, U1.5 (+)
unnamed: C10.1, R13.2
unnamed: D1.2 (A), V_IN.1 (+)
unnamed: R3.1, R4.1, U1.2 (-)
unnamed: R7.1, R8.1, U1.6 (-)
unnamed: R11.1, U2.1, U2.2 (-)
unnamed: R13.1, U2.6 (-), U2.7
unnamed: R23.1, R_GPIO.2
unnamed: R_GPIO.1, V_GPIO.1 (+)
unnamed: R_S.1, V_IF.1 (+)
unnamed: X1.1, X2.1 (IN)
TP_AOUT: C2.1, R3.2, U1.1
TP_AP: C1.2, R2.1, U1.3 (+)
TP_AUDIO: C10.2, R14.1, R_LOAD.1
TP_BEAT: C2.2, R6.1
TP_BOUT: R7.2, R12.1, U1.7
TP_IF: C1.1, C20.1, R1.1, R_S.2
TP_LP: C9.1, R12.2, U2.5 (+)
TP_SC: C_CPL.2, R_SC.1
TP_SYNC: C_CPL.1, R23.2, R24.1
TP_VANA: C13.1, R15.2, R_OPAMPS.1
TP_VDIV: C5.1, R9.2, R10.1, U2.3 (+)
TP_VPROT: C11.1, D1.1 (K), R15.1, R_BUCK.1
TP_VREF: C6.1, R11.2, R_LOAD.1
TX: A3.3 (OUT), A4.1 (X), A4.2 (Y), T1.1 (IN), T2.1 (IN), X2.2 (OUT)
VANA: C3.1, C7.1, R9.1, U1.8 (V+), U2.8 (V+), V_ANA.1 (+)
VREF: C9.2, R2.2, R4.2, R6.2, R8.2, V_REF.1 (+)

Notes on the sheet:
1 · VIDEO AMPLIFIER — mixer IF in, sound-card line out. Probe TP_IF TP_AP TP_AOUT TP_BOUT TP_LP TP_AUDIO
V_IF: Multisim AC_VOLTAGE. 10 mVpk for the low-gain build,
0.5 mVpk for full gain (it clips at 10 mV). Bode: AC sweep 1 Hz-100 kHz
mixer IF source impedance
gain A = 1 + R3/R4 = 101 (R4 = 4.7k -> 22, first power-up)
gain B = 1 + R7/R8 = 11 (R7 = wire link -> 1)
R12/C9: 15.9 kHz low-pass
R_LOAD = sound-card line input
(or drive VREF from frame 2)
EXPECTED low gain (R4 4.7k, R7 link): 10 mVpk in -> 107 mVpk at TP_AUDIO
full gain: 54.6 dB from V_IF at 1 kHz, -6 dB at 159 Hz, -3 dB at 15.9 kHz; clips at +/-4.1 V
radar input 8 mV @ 12.5 Hz + 40 uV @ 417 Hz -> TP_AUDIO 27 mV leak, 19 mV echo
U1A/U1B/U2B = TL072CP (Multisim: Analog > OPAMP > TL072CP)
2 · HALF-RAIL REFERENCE — VREF = VANA/2 buffered
ripple test: + 100 mVpk 150 kHz
R_LOAD = the six VREF returns
EXPECTED TP_VDIV 5.70 V, TP_VREF 5.70 V, ripple at TP_VREF < 1 uV
3 · 12 V INPUT — D1 -> VPROT -> R15/C13 -> VANA
ripple test: + 100 mVpk 150 kHz; reverse test: -12 V
60 R = the LM2596 drawing 0.2 A
1.1k = two TL072 + dividers
EXPECTED TP_VPROT 11.7 V, TP_VANA 11.6 V, ripple 4 mVpp;
with V_IN = -12 V: TP_VPROT -0.1 mV, 2 uA
4 · SYNC DIVIDER — ESP32 GPIO -> 0.3 V -> sound-card R
6.4 ms high, 7.4 ms period, 10 ns edges
GPIO output R
C_CPL / R_SC = the sound card's AC-coupled input
EXPECTED TP_SYNC 283 mV high / 0 V low;
TP_SC +201 mV drooping / -100 mV retrace pulse -> software detects EDGES
5 · THE RADAR ITSELF, SCALED — chirp x delayed chirp = beat. Carrier cancels, so B/10 and delay x10 give the real 417 Hz
R12/C9 = the amp's 15.9 kHz LP; C1/R2, C2/R6 = its two 159 Hz HPs (they kill the leakage tone)
Multisim parts: PIECEWISE_LINEAR_VOLTAGE -> VOLTAGE_CONTROLLED_SINE_WAVE; LOSSLESS_LINE_TYPE1; VOLTAGE_GAIN_BLOCK; VOLTAGE_SUMMER; MULTIPLIER
Transient: TMAX 10 ns, stop 19.2 ms (3 chirps). Fourier at TP_BEAT over ONE chirp (6.4 ms), Hanning window.
EXPECTED leakage gain x0: peak at 417 Hz, 4.5 mV. TD1 = 333 ns -> 208 Hz. TD1 = 1.33 us -> 833 Hz (20 m).
Leakage gain x1: the 417 Hz line is unchanged but the spectrum floor rises 20 dB near DC - what chirp-to-chirp subtraction removes in software.
Real radar: B = 40 MHz, TD = 66.7 ns (10 m), T = 6.4 ms -> f_beat = B x TD / T = 417 Hz. Here: B = 4 MHz, TD = 667 ns. Same answer.
The blocks right of the mixer's IF port cannot be simulated in Multisim (no 2.4 GHz models): ADF4351, SPF5189Z, splitter, mixer, horns are measured, not modelled.
PARTS resistors 1 % 1/4 W · 100n / 10n film or C0G · 10u 47u 100u electrolytic 25 V (+ marked) · 1N5822 · TL072CP x3 · single 12 V rail
Netlists that produced the EXPECTED lines: hardware/spice/*.cir (ngspice 42). Same values as the breadboard sheet radar_breadboard.kicad_sch.
